omarwatt/MCU-with-Peripherals/DUT/EXECUTE.VHD

--============================================================================
-- Copyright 2026 Hananya Ribo 
-- Advanced CPU architecture and Hardware Accelerators Lab 361-1-4693 BGU
-- Execute module (implements the data ALU and Branch Address Adder) 
--============================================================================
LIBRARY IEEE;
USE IEEE.STD_LOGIC_1164.ALL;
USE IEEE.STD_LOGIC_ARITH.ALL;
USE IEEE.STD_LOGIC_SIGNED.ALL;
USE IEEE.NUMERIC_STD.ALL;
USE work.const_package.all;


ENTITY  Execute IS
	generic(
		DATA_BUS_WIDTH 	: integer := 32;
		MULT_WIDTH	 	: integer := 16;
		PC_WIDTH 		: integer := 10
	);
	PORT(	
		--Inputs
		read_data1_i 	: IN 	STD_LOGIC_VECTOR(DATA_BUS_WIDTH-1 DOWNTO 0);
		read_data2_i 	: IN 	STD_LOGIC_VECTOR(DATA_BUS_WIDTH-1 DOWNTO 0);
		sign_extend_i 	: IN 	STD_LOGIC_VECTOR(DATA_BUS_WIDTH-1 DOWNTO 0);
		UpperIm_ctrl_i	: IN 	STD_LOGIC_VECTOR(1 DOWNTO 0);
		ALUOp_ctrl_i	: IN 	STD_LOGIC_VECTOR(4 DOWNTO 0);
		MULOp_ctrl_i	: IN 	STD_LOGIC_VECTOR(1 DOWNTO 0);
		ALUSrc_ctrl_i 	: IN 	STD_LOGIC;
		pc_i			: IN 	STD_LOGIC_VECTOR(PC_WIDTH-1 DOWNTO 0);
		--Outputs
		brTaken_o 		: OUT	STD_LOGIC;
		mul_res_o 		: OUT	STD_LOGIC_VECTOR(DATA_BUS_WIDTH-1 DOWNTO 0);
		alu_res_o 		: OUT	STD_LOGIC_VECTOR(DATA_BUS_WIDTH-1 DOWNTO 0);
		addr_gen_o 		: OUT	STD_LOGIC_VECTOR(PC_WIDTH-1 DOWNTO 0)
	);
END Execute;


ARCHITECTURE struct OF Execute IS
	SIGNAL 	ain_w 					: STD_LOGIC_VECTOR(DATA_BUS_WIDTH-1 DOWNTO 0);
	SIGNAL 	bin_w 					: STD_LOGIC_VECTOR(DATA_BUS_WIDTH-1 DOWNTO 0);
	SIGNAL 	sub_res_w 			: STD_LOGIC_VECTOR(DATA_BUS_WIDTH-1 DOWNTO 0);
	SIGNAL 	ltu_res_w 			: STD_LOGIC;
	SIGNAL 	eq_res_w				: STD_LOGIC;
	SIGNAL	msbneq_res_w		: STD_LOGIC;
	SIGNAL	alu_res_r 			: STD_LOGIC_VECTOR(DATA_BUS_WIDTH-1 DOWNTO 0);
	SIGNAL	brTaken_w 			: STD_LOGIC;
	
	SIGNAL	brl_shl_s1_r		: STD_LOGIC_VECTOR(DATA_BUS_WIDTH-1 DOWNTO 0);
	SIGNAL	brl_shl_s2_r		: STD_LOGIC_VECTOR(DATA_BUS_WIDTH-1 DOWNTO 0);
	SIGNAL	brl_shl_s3_r		: STD_LOGIC_VECTOR(DATA_BUS_WIDTH-1 DOWNTO 0);
	SIGNAL	brl_shl_s4_r		: STD_LOGIC_VECTOR(DATA_BUS_WIDTH-1 DOWNTO 0);
	
	SIGNAL	brl_shr_s1_r		: STD_LOGIC_VECTOR(DATA_BUS_WIDTH-1 DOWNTO 0);
	SIGNAL	brl_shr_s2_r		: STD_LOGIC_VECTOR(DATA_BUS_WIDTH-1 DOWNTO 0);
	SIGNAL	brl_shr_s3_r		: STD_LOGIC_VECTOR(DATA_BUS_WIDTH-1 DOWNTO 0);
	SIGNAL	brl_shr_s4_r		: STD_LOGIC_VECTOR(DATA_BUS_WIDTH-1 DOWNTO 0);
	SIGNAL	brl_shr_pad_r		: STD_LOGIC_VECTOR(DATA_BUS_WIDTH-1 DOWNTO 0);
	
	SIGNAL P0_w, P1_w, P2_w, P3_w 	: STD_LOGIC_VECTOR(MULT_WIDTH-1 downto 0);
	SIGNAL al_w, ah_w, bl_w, bh_w 	: STD_LOGIC_VECTOR(7 downto 0);
	SIGNAL M_w 						: STD_LOGIC_VECTOR(16 downto 0);
	SIGNAL MULTI_res_r				: std_logic_vector(DATA_BUS_WIDTH-1 DOWNTO 0);
		
BEGIN
--------------------------------------------------------------------------------------------------------
-- Branch Address Adder
-- addr_gen_o = pc_i + (sign_extend_i << 2)
--------------------------------------------------------------------------------------------------------					  
addr_gen_o	<= pc_i(PC_WIDTH-1 DOWNTO 0) + (sign_extend_i(PC_WIDTH-3 DOWNTO 0) & '0');

--------------------------------------------------------------------------------------------------------
--ALU
--------------------------------------------------------------------------------------------------------
WITH UpperIm_ctrl_i SELECT
	ain_w <= 	read_data1_i																					WHEN	"00",
						((DATA_BUS_WIDTH-PC_WIDTH-1) DOWNTO 0 => '0') & pc_i	WHEN	"01",
						(others => '0')	WHEN	OTHERS;
	
bin_w <= 	read_data2_i	WHEN not ALUSrc_ctrl_i ELSE	sign_extend_i(DATA_BUS_WIDTH-1 DOWNTO 0);


--Reused resuls 
sub_res_w			<= ain_w - bin_w;
ltu_res_w			<= '1' WHEN ain_w < bin_w 					ELSE '0';
eq_res_w			<= '1' WHEN ain_w = bin_w 					ELSE '0'; 
msbneq_res_w		<= '1' WHEN ain_w(31) /= bin_w(31) 	ELSE '0';


al_w <= ain_w(7  downto 0)	when MULOp_ctrl_i = Multi_Mul else (others => '0');
ah_w <= ain_w(15 downto 8) 	when MULOp_ctrl_i = Multi_Mul else (others => '0');
bl_w <= bin_w(7  downto 0) 	when MULOp_ctrl_i = Multi_Mul else (others => '0');
bh_w <= bin_w(15 downto 8) 	when MULOp_ctrl_i = Multi_Mul else (others => '0');

P0_w <= al_w * bl_w;
P1_w <= al_w * bh_w;
P2_w <= ah_w * bl_w;
P3_w <= ah_w * bh_w;
M_w  <= ('0' & P1_w) + ('0' & P2_w);

PROCESS (all)
BEGIN
	-- default values
	alu_res_r 		<= (others => '0');
	MULTI_res_r 	<= (others => '0');
	brTaken_w 		<= '0';
	brl_shl_s1_r	<= (others => '0');
	brl_shl_s2_r	<= (others => '0');
	brl_shl_s3_r	<= (others => '0'); 
	brl_shl_s4_r	<= (others => '0');
	brl_shr_s1_r	<= (others => '0');
	brl_shr_s2_r	<= (others => '0');
	brl_shr_s3_r	<= (others => '0'); 
	brl_shr_s4_r	<= (others => '0');
	brl_shr_pad_r	<= (others => '0');
	
	
 	CASE ALUOp_ctrl_i IS	-- Select ALU operation
		------------------------------------------------------
    -- Arithmetic
    ------------------------------------------------------
		-- add, addi, auipc, jal, jalr
		WHEN ALU_ADD 	=>
			alu_res_r	<= ain_w + bin_w;
			brTaken_w	<= '0';
		
		-- sub
		WHEN ALU_SUB	=>
			alu_res_r	<= sub_res_w;		 
			brTaken_w	<= '0';
		------------------------------------------------------
    -- Logic
    ------------------------------------------------------
		-- and, andi	
    WHEN	ALU_AND 	=>
			alu_res_r	<= ain_w and bin_w;
			brTaken_w	<= '0';
		
		-- or, ori		
	 	WHEN ALU_OR	=>
			alu_res_r	<= ain_w or bin_w;
			brTaken_w	<= '0';
		
		-- xor, xori
		WHEN ALU_XOR 	=>
			alu_res_r	<= ain_w xor bin_w;
			brTaken_w	<= '0';
				
		------------------------------------------------------
    -- Shift Left
    ------------------------------------------------------
		-- sll, slli
 	 	WHEN ALU_SHIFTL	=>
			-- Barrel-Shifter SHL stage 0
			if (bin_w(0) = '1') then
				brl_shl_s1_r <= (ain_w(30 DOWNTO 0) & '0');
			else
				brl_shl_s1_r <= ain_w;
			end if;
					
			-- Barrel-Shifter SHL stage 1
			if (bin_w(1) = '1') then
				brl_shl_s2_r <= (brl_shl_s1_r(29 DOWNTO 0) & "00");
			else
				brl_shl_s2_r <= brl_shl_s1_r;
			end if;
					
			-- Barrel-Shifter SHL stage 2
			if (bin_w(2) = '1')	then
				brl_shl_s3_r <= (brl_shl_s2_r(27 DOWNTO 0) & "0000");
			else
				brl_shl_s3_r <= brl_shl_s2_r;
			end if;
					
			-- Barrel-Shifter SHL stage 3
			if (bin_w(3) = '1')	then
				brl_shl_s4_r <= (brl_shl_s3_r(23 DOWNTO 0) & "00000000");
			else
				brl_shl_s4_r <= brl_shl_s3_r;
			end if;
					
			-- Barrel-Shifter SHL stage 4
			if (bin_w(4) = '1')	then
				alu_res_r <= (brl_shl_s4_r(15 DOWNTO 0) & "0000000000000000");
			else
				alu_res_r <= brl_shl_s4_r;
			end if;
				      
			brTaken_w	<= '0';
		------------------------------------------------------
    -- Shift Right
    ------------------------------------------------------		
		-- srl, srli, sra, srai	
 	 	WHEN ALU_SHIFTR | ALU_SHIFTR_ARITH 	=>
			--if sra? pad with 1's else pad with 0's 
			if (ain_w(31) = '1' and (ALUOp_ctrl_i = ALU_SHIFTR_ARITH)) then
				brl_shr_pad_r <= 32x"FFFF";
			else
				brl_shr_pad_r <= 32x"0000";
			end if;
			
			-- Barrel-Shifter SHR stage 0
			if (bin_w(0) = '1') then
				brl_shr_s1_r <= (brl_shr_pad_r(31) & ain_w(31 DOWNTO 1));
			else
				brl_shr_s1_r <= ain_w;
			end if;
			
			-- Barrel-Shifter SHR stage 1
			if (bin_w(1) = '1') then
				brl_shr_s2_r <= (brl_shr_pad_r(31 DOWNTO 30) & brl_shr_s1_r(31 DOWNTO 2));
			else
				brl_shr_s2_r <= brl_shr_s1_r;
			end if;
			
			-- Barrel-Shifter SHR stage 2
			if (bin_w(2) = '1') then
				brl_shr_s3_r <= (brl_shr_pad_r(31 DOWNTO 28) & brl_shr_s2_r(31 DOWNTO 4));
			else
				brl_shr_s3_r <= brl_shr_s2_r;
			end if;
			
			-- Barrel-Shifter SHR stage 3
			if (bin_w(3) = '1') then
				brl_shr_s4_r <= (brl_shr_pad_r(31 DOWNTO 24) & brl_shr_s3_r(31 DOWNTO 8));
			else
				brl_shr_s4_r <= brl_shr_s3_r;
			end if;
			
			-- Barrel-Shifter SHR stage 4
			if (bin_w(4) = '1')	then
				alu_res_r <= (brl_shr_pad_r(31 DOWNTO 16) & brl_shr_s4_r(31 DOWNTO 16));
			else
				alu_res_r <= brl_shr_s4_r;
			end if;
				   
			brTaken_w	<= '0';		 	 				
		------------------------------------------------------
    -- Comparision
    ------------------------------------------------------
		-- slt, slti
		WHEN ALU_LESS_THAN_SIGNED	=>
			brTaken_w	<= '0';
			IF msbneq_res_w THEN
				IF ain_w(31) THEN
					alu_res_r	<= (0 => '1', others => '0');	--32'h1
				ELSE
					alu_res_r	<= (others => '0');						--32'h0
				END IF;
			ELSE
				IF sub_res_w(31) THEN
					alu_res_r	<= (0 => '1', others => '0');	--32'h1	
				ELSE
					alu_res_r	<= (others => '0');						--32'h0
				END IF;
			END IF;
		
		-- sltu, sltiu 
		WHEN ALU_LESS_THAN_UNSIGNED	=>
			brTaken_w	<= '0';
			IF ltu_res_w THEN
				alu_res_r	<= (0 => '1', others => '0');		--32'h1
			ELSE
				alu_res_r	<= (others => '0');							--32'h0
			END IF;

	------------------------------------------------------
    -- Condional Branch 
    ------------------------------------------------------
		-- beq
		WHEN ALU_BEQ	=>
			alu_res_r	<= (others => '0');
			brTaken_w	<= eq_res_w;
		
		-- bne
		WHEN ALU_BNE	=>
			alu_res_r	<= (others => '0');
			brTaken_w	<= not eq_res_w;
		
		-- blt
		WHEN ALU_BLT	=>
			alu_res_r	<= (others => '0');
			IF msbneq_res_w THEN
				brTaken_w	<= ain_w(31);
			ELSE
				brTaken_w	<= sub_res_w(31);
			END IF;
		
		-- bge
		WHEN ALU_BGE	=>
			alu_res_r	<= (others => '0');
			IF msbneq_res_w THEN
				brTaken_w	<= bin_w(31);
			ELSE
				brTaken_w	<= not sub_res_w(31);
			END IF;
		
		-- bltu
		WHEN ALU_BLTU	=>
			alu_res_r	<= (others => '0');
			brTaken_w	<= ltu_res_w;
		
		-- bgeu
		WHEN ALU_BGEU	=>
			alu_res_r	<= (others => '0');
			brTaken_w	<= not ltu_res_w;
		
 	 	WHEN OTHERS	=>
			alu_res_r	<= (others => '0');
			brTaken_w	<= '0';
  	END CASE;

	case MULOp_ctrl_i is
		when  Multi_Mul =>
			MULTI_res_r <= (X"0000" & P0_w) + ("0000000" & M_w & x"00") + (P3_w & x"0000");
		when others =>
			MULTI_res_r <= (others => '0');
	end case;

		
  
END PROCESS;
	
--------------------------------------------------------------------------------------------------------
brTaken_o	<= brTaken_w;

alu_res_o <= alu_res_r;

mul_res_o <= MULTI_res_r;


END struct;
