omarwatt/MCU-with-Peripherals/DUT/uart_rx.vhd

--------------------------------------------------------------------------------
-- PROJECT: SIMPLE UART FOR FPGA
--------------------------------------------------------------------------------
-- MODULE:  UART RECEIVER
-- AUTHORS: Jakub Cabal <jakubcabal@gmail.com>
-- LICENSE: The MIT License (MIT), please read LICENSE file
-- WEBSITE: https://github.com/jakubcabal/uart-for-fpga
--------------------------------------------------------------------------------

library IEEE;
use IEEE.STD_LOGIC_1164.ALL;
use IEEE.NUMERIC_STD.ALL;
use work.aux_package.all;

entity UART_RX is
    Port (
        CLK         : in  std_logic; -- system clock
        RST         : in  std_logic; -- high active synchronous reset
        -- UART INTERFACE
        UART_CLK_EN : in  std_logic; -- oversampling (16x) UART clock enable
        UART_RXD    : in  std_logic; -- serial receive data
        PENA_i      : in  std_logic; -- ADDED: UTCL parity enable
        PEV_i       : in  std_logic; -- ADDED: UTCL parity type
        -- USER DATA OUTPUT INTERFACE
        DOUT            : out std_logic_vector(7 downto 0); -- output data received via UART
        DOUT_VLD        : out std_logic; -- when DOUT_VLD = 1, output data (DOUT) are valid (is assert only for one clock cycle)
        FRAME_ERROR     : out std_logic;  -- when FRAME_ERROR = 1, stop bit was invalid (is assert only for one clock cycle)
        PARITY_ERROR    : out std_logic; 
        RX_BUSY_o       : out std_logic  
    );
end UART_RX;

architecture FULL of UART_RX is

    signal rx_clk_en          : std_logic;
    signal rx_ticks           : unsigned(3 downto 0);
    signal rx_clk_divider_en  : std_logic;
    signal rx_data            : std_logic_vector(7 downto 0);
    signal rx_bit_count       : unsigned(2 downto 0);
    signal rx_receiving_data  : std_logic;
    signal rx_parity_bit      : std_logic;
    signal rx_parity_error    : std_logic;
    signal rx_output_reg_en   : std_logic;


    type state is (idle, startbit, databits, paritybit, stopbit);
    signal rx_pstate : state;
    signal rx_nstate : state;

begin

    DOUT <= rx_data;
    RX_BUSY_o   <= '0' when rx_pstate = idle else '1';
    -- -------------------------------------------------------------------------
    -- UART RECEIVER CLOCK DIVIDER AND CLOCK ENABLE FLAG
    -- -------------------------------------------------------------------------
    uart_rx_clk_divider_p : process (CLK)
    begin
        if (rising_edge(CLK)) then
            if (rx_clk_divider_en = '1') then
                if (UART_CLK_EN = '1') then
                    if (rx_ticks = "1111") then
                        rx_ticks <= (others => '0');
                    else
                        rx_ticks <= rx_ticks + 1;
                    end if;
                else
                    rx_ticks <= rx_ticks;
                end if;
            else
                rx_ticks <= (others => '0');
            end if;
        end if;
    end process;

    uart_rx_clk_en_p : process (CLK)
    begin
        if (rising_edge(CLK)) then
            if (RST = '1') then
                rx_clk_en <= '0';
            elsif (UART_CLK_EN = '1' AND rx_ticks = "0111") then
                rx_clk_en <= '1';
            else
                rx_clk_en <= '0';
            end if;
        end if;
    end process;
    
    -- -------------------------------------------------------------------------
    -- UART RECEIVER BIT COUNTER
    -- -------------------------------------------------------------------------

    uart_rx_bit_counter_p : process (CLK)
    begin
        if (rising_edge(CLK)) then
            if (RST = '1') then
                rx_bit_count <= (others => '0');
            elsif (rx_clk_en = '1' AND rx_receiving_data = '1') then
                if (rx_bit_count = "111") then
                    rx_bit_count <= (others => '0');
                else
                    rx_bit_count <= rx_bit_count + 1;
                end if;
            end if;
        end if;
    end process;

    -- -------------------------------------------------------------------------
    -- UART RECEIVER DATA SHIFT REGISTER
    -- -------------------------------------------------------------------------

    uart_rx_data_shift_reg_p : process (CLK)
    begin
        if (rising_edge(CLK)) then
            if RST = '1' then
                rx_data <= (others => '0'); 
            elsif (rx_clk_en = '1' AND rx_receiving_data = '1') then
                rx_data <= UART_RXD & rx_data(7 downto 1);
            end if;
        end if;
    end process;


    -- -------------------------------------------------------------------------
    -- UART RECEIVER PARITY GENERATOR AND CHECK
    -- -------------------------------------------------------------------------

    uart_rx_parity_gen_i : entity work.UART_PARITY
        generic map (
            DATA_WIDTH => 8
        )
        port map (
            DATA_IN    => rx_data,
            PEV_i      => PEV_i,
            PARITY_OUT => rx_parity_bit
        ); 

    uart_rx_parity_check_reg_p : process (CLK)
    begin
        if (rising_edge(CLK)) then
            if (PENA_i = '0') then
                rx_parity_error <= '0';
            elsif (rx_clk_en = '1') then
                rx_parity_error <= rx_parity_bit XOR UART_RXD;
            end if;
        end if;
    end process;

    -- -------------------------------------------------------------------------
    -- UART RECEIVER OUTPUT REGISTER
    -- -------------------------------------------------------------------------

    uart_rx_output_reg_p : process (CLK)
    begin
        if (rising_edge(CLK)) then
            if (RST = '1') then
                DOUT_VLD        <= '0';
                FRAME_ERROR     <= '0';
                PARITY_ERROR    <= '0';
            else
                if (rx_clk_en = '1' AND rx_output_reg_en = '1') then
                    DOUT_VLD <= '1';
                    FRAME_ERROR <= NOT UART_RXD;
                    if PENA_i = '1' then
                        PARITY_ERROR <= rx_parity_error; -- make the error seperate from dout_vld
                    else
                        PARITY_ERROR <= '0';
                    end if;
                else
                    DOUT_VLD        <= '0';
                    FRAME_ERROR     <= '0';
                    PARITY_ERROR    <= '0';
                end if;
            end if;
        end if;
    end process;

    -- -------------------------------------------------------------------------
    -- UART RECEIVER FSM
    -- -------------------------------------------------------------------------

    -- PRESENT STATE REGISTER
    process (CLK)
    begin
        if (rising_edge(CLK)) then
            if (RST = '1') then
                rx_pstate <= idle;
            else
                rx_pstate <= rx_nstate;
            end if;
        end if;
    end process;

    -- NEXT STATE AND OUTPUTS LOGIC
    process (all)
    begin
        case rx_pstate is

            when idle =>
                rx_output_reg_en  <= '0';
                rx_receiving_data <= '0';
                rx_clk_divider_en <= '0';

                if (UART_RXD = '0') then
                    rx_nstate <= startbit;
                else
                    rx_nstate <= idle;
                end if;

            when startbit =>
                rx_output_reg_en  <= '0';
                rx_receiving_data <= '0';
                rx_clk_divider_en <= '1';

                if (rx_clk_en = '1') then
                    rx_nstate <= databits;
                else
                    rx_nstate <= startbit;
                end if;

            when databits =>
                rx_output_reg_en  <= '0';
                rx_receiving_data <= '1';
                rx_clk_divider_en <= '1';

                if ((rx_clk_en = '1') AND (rx_bit_count = "111")) then
                    if (PENA_i = '0') then
                        rx_nstate <= stopbit;
                    else
                        rx_nstate <= paritybit;
                    end if ;
                else
                    rx_nstate <= databits;
                end if;

            when paritybit =>
                rx_output_reg_en  <= '0';
                rx_receiving_data <= '0';
                rx_clk_divider_en <= '1';

                if (rx_clk_en = '1') then
                    rx_nstate <= stopbit;
                else
                    rx_nstate <= paritybit;
                end if;

            when stopbit =>
                rx_output_reg_en  <= '1';
                rx_receiving_data <= '0';
                rx_clk_divider_en <= '1';

                if (rx_clk_en = '1') then
                    rx_nstate <= idle;
                else
                    rx_nstate <= stopbit;
                end if;

            when others =>
                rx_output_reg_en  <= '0';
                rx_receiving_data <= '0';
                rx_clk_divider_en <= '0';
                rx_nstate         <= idle;

        end case;
    end process;

end FULL;
