omarwatt/MCU-with-Peripherals/DUT/uart_tx.vhd

--------------------------------------------------------------------------------
-- PROJECT: SIMPLE UART FOR FPGA
--------------------------------------------------------------------------------
-- MODULE:  UART TRANSMITTER
-- AUTHORS: Jakub Cabal <jakubcabal@gmail.com>
-- LICENSE: The MIT License (MIT), please read LICENSE file
-- WEBSITE: https://github.com/jakubcabal/uart-for-fpga
--------------------------------------------------------------------------------

library IEEE;
use IEEE.STD_LOGIC_1164.ALL;
use IEEE.NUMERIC_STD.ALL;
use work.aux_package.all;

entity UART_TX is
    Port (
        CLK         : in  std_logic; -- system clock
        RST         : in  std_logic; -- high active synchronous reset
        -- UART INTERFACE
        UART_CLK_EN : in  std_logic; -- oversampling (16x) UART clock enable
        UART_TXD    : out std_logic; -- serial transmit data
        -- USER DATA INPUT INTERFACE
        DIN         : in  std_logic_vector(7 downto 0); -- input data to be transmitted over UART
        DIN_VLD     : in  std_logic; -- when DIN_VLD = 1, input data (DIN) are valid
        DIN_RDY     : out std_logic;  -- when DIN_RDY = 1, transmitter is ready and valid input data will be accepted for transmiting
       
        PENA_i        : in  std_logic; 
        PEV_i         : in  std_logic;
        TX_BUSY_o     : out std_logic
    );
end UART_TX;

architecture FULL of UART_TX is

    signal tx_clk_en         : std_logic;
    signal tx_clk_divider_en : std_logic;
    signal tx_ticks          : unsigned(3 downto 0);
    signal tx_data           : std_logic_vector(7 downto 0);
    signal tx_bit_count      : unsigned(2 downto 0);
    signal tx_bit_count_en   : std_logic;
    signal tx_ready          : std_logic;
    signal tx_parity_bit     : std_logic;
    signal tx_data_out_sel   : std_logic_vector(1 downto 0);

    type state is (idle, txsync, startbit, databits, paritybit, stopbit);
    signal tx_pstate : state;
    signal tx_nstate : state;

begin

    DIN_RDY     <= tx_ready;
    TX_BUSY_o   <= '0' when tx_pstate = idle else '1';
    -- -------------------------------------------------------------------------
    -- UART TRANSMITTER CLOCK DIVIDER
    -- -------------------------------------------------------------------------

    uart_tx_clk_divider_p : process (CLK)
    begin
        if (rising_edge(CLK)) then
            if (tx_clk_divider_en = '1') then
                if (uart_clk_en = '1') then
                    if (tx_ticks = "1111") then
                        tx_ticks <= (others => '0');
                    else
                        tx_ticks <= tx_ticks + 1;
                    end if;
                else
                    tx_ticks <= tx_ticks;
                end if;
            else
                tx_ticks <= (others => '0');
            end if;
        end if;
    end process;

    uart_tx_clk_en_p : process (CLK)
    begin
        if (rising_edge(CLK)) then
            if (RST = '1') then
                tx_clk_en <= '0';
            elsif (uart_clk_en = '1' AND tx_ticks = "0001") then
                tx_clk_en <= '1';
            else
                tx_clk_en <= '0';
            end if;
        end if;
    end process;

    -- -------------------------------------------------------------------------
    -- UART TRANSMITTER INPUT DATA REGISTER
    -- -------------------------------------------------------------------------

    uart_tx_input_data_reg_p : process (CLK)
    begin
        if (rising_edge(CLK)) then
            if RST = '1' then
                tx_data     <= (others => '0') ;
            elsif (DIN_VLD = '1' AND tx_ready = '1') then
                tx_data     <= DIN;
            end if;
        end if;
    end process;
    -- -------------------------------------------------------------------------
    -- UART TRANSMITTER BIT COUNTER
    -- -------------------------------------------------------------------------

    uart_tx_bit_counter_p : process (CLK)
    begin
        if (rising_edge(CLK)) then
            if (RST = '1') then
                tx_bit_count <= (others => '0');
            elsif (tx_bit_count_en = '1' AND tx_clk_en = '1') then
                if (tx_bit_count = "111") then
                    tx_bit_count <= (others => '0');
                else
                    tx_bit_count <= tx_bit_count + 1;
                end if;
            end if;
        end if;
    end process;

    -- -------------------------------------------------------------------------
    -- UART TRANSMITTER PARITY GENERATOR
    -- -------------------------------------------------------------------------

        uart_tx_parity_gen_i: entity work.UART_PARITY
        generic map (
            DATA_WIDTH  => 8
        )
        port map (
            DATA_IN     => tx_data,
            PEV_i       => PEV_i,
            PARITY_OUT  => tx_parity_bit
        );
   

    -- uart_tx_noparity_g : if (PARITY_BIT = "none") generate
    --     tx_parity_bit <= '0';
    -- end generate;

    -- -------------------------------------------------------------------------
    -- UART TRANSMITTER OUTPUT DATA REGISTER
    -- -------------------------------------------------------------------------

    uart_tx_output_data_reg_p : process (CLK)
    begin
        if (rising_edge(CLK)) then
            if (RST = '1') then
                UART_TXD <= '1';
            else
                case tx_data_out_sel is
                    when "01" => -- START BIT
                        UART_TXD <= '0';
                    when "10" => -- DATA BITS
                        UART_TXD <= tx_data(to_integer(tx_bit_count));
                    when "11" => -- PARITY BIT
                        UART_TXD <= tx_parity_bit;
                    when others => -- STOP BIT OR IDLE
                        UART_TXD <= '1';
                end case;
            end if;
        end if;
    end process;

    -- -------------------------------------------------------------------------
    -- UART TRANSMITTER FSM
    -- -------------------------------------------------------------------------

    -- PRESENT STATE REGISTER
    process (CLK)
    begin
        if (rising_edge(CLK)) then
            if (RST = '1') then
                tx_pstate <= idle;
            else
                tx_pstate <= tx_nstate;
            end if;
        end if;
    end process;

    -- NEXT STATE AND OUTPUTS LOGIC
    process (all)
    begin

        case tx_pstate is

            when idle =>
                tx_ready <= '1';
                tx_data_out_sel <= "00";
                tx_bit_count_en <= '0';
                tx_clk_divider_en <= '0';

                if (DIN_VLD = '1') then
                    tx_nstate <= txsync;
                else
                    tx_nstate <= idle;
                end if;

            when txsync =>
                tx_ready <= '0';
                tx_data_out_sel <= "00";
                tx_bit_count_en <= '0';
                tx_clk_divider_en <= '1';

                if (tx_clk_en = '1') then
                    tx_nstate <= startbit;
                else
                    tx_nstate <= txsync;
                end if;

            when startbit =>
                tx_ready <= '0';
                tx_data_out_sel <= "01";
                tx_bit_count_en <= '0';
                tx_clk_divider_en <= '1';

                if (tx_clk_en = '1') then
                    tx_nstate <= databits;
                else
                    tx_nstate <= startbit;
                end if;

            when databits =>
                tx_ready <= '0';
                tx_data_out_sel <= "10";
                tx_bit_count_en <= '1';
                tx_clk_divider_en <= '1';

                if ((tx_clk_en = '1') AND (tx_bit_count = "111")) then
                    if (PENA_i = '1') then
                        tx_nstate <= paritybit;
                    else
                        tx_nstate <= stopbit;
                    end if ;
                else
                    tx_nstate <= databits;
                end if;

            when paritybit =>
                tx_ready <= '0';
                tx_data_out_sel <= "11";
                tx_bit_count_en <= '0';
                tx_clk_divider_en <= '1';

                if (tx_clk_en = '1') then
                    tx_nstate <= stopbit;
                else
                    tx_nstate <= paritybit;
                end if;

            when stopbit =>
                tx_ready <= '0';
                tx_data_out_sel <= "00";
                tx_bit_count_en <= '0';
                tx_clk_divider_en <= '1';

                if (tx_clk_en = '1') then
                    tx_nstate <= idle;
                else
                    tx_nstate <= stopbit;
                end if;

            when others =>
                tx_ready <= '0';
                tx_data_out_sel <= "00";
                tx_bit_count_en <= '0';
                tx_clk_divider_en <= '0';
                tx_nstate <= idle;

        end case;
    end process;

end FULL;
