omarwatt/MCU-with-Peripherals/TB/BasicTimer_tb.vhd

library ieee;
use ieee.std_logic_1164.all;

entity BasicTimer_tb is
end BasicTimer_tb;

architecture sim of BasicTimer_tb is

    signal SMCLK        : std_logic := '0';
    signal rst          : std_logic := '1';
    signal Address      : std_logic_vector(5 downto 0) := (others => '0');
    signal MemRead      : std_logic := '0';
    signal MemWrite     : std_logic := '0';
    signal CAPIN1       : std_logic := '0';
    signal CAPIN2       : std_logic := '0';

    signal DataBus      : std_logic_vector(31 downto 0);
    signal TB_Data      : std_logic_vector(31 downto 0) := (others => '0');
    signal TB_BusEnable : std_logic := '0';

    signal PWM          : std_logic;
    signal BTIFG        : std_logic;
    signal BTCAPR       : std_logic_vector(31 downto 0);

begin

    SMCLK <= not SMCLK after 5 ns;

    DataBus <= TB_Data when TB_BusEnable = '1'
               else (others => 'Z');

    DUT : entity work.BasicTimer
        port map (
            SMCLK_i    => SMCLK,
            rst_i      => rst,
            Address_i  => Address,
            DataBus_io => DataBus,
            MemRead_i  => MemRead,
            MemWrite_i => MemWrite,
            CAPIN1_i   => CAPIN1,
            CAPIN2_i   => CAPIN2,
            PWM_o      => PWM,
            BTIFG_o    => BTIFG,
            BTCAPR_o   => BTCAPR
        );

    process
    begin
        --------------------------------------------------
        -- Test 1: BTCMPR0 = 2
        --------------------------------------------------
        rst <= '1';
        wait for 20 ns;
        rst <= '0';

        Address      <= "110000";
        TB_Data      <= x"00000002";
        TB_BusEnable <= '1';
        MemWrite     <= '1';
        wait until falling_edge(SMCLK);
        MemWrite     <= '0';
        TB_BusEnable <= '0';

        Address      <= "101110";
        TB_Data      <= x"00000000";
        TB_BusEnable <= '1';
        MemWrite     <= '1';
        wait until falling_edge(SMCLK);
        MemWrite     <= '0';
        TB_BusEnable <= '0';

        wait for 220 ns;

        --------------------------------------------------
        -- Test 2: BTCMPR0 = 4
        --------------------------------------------------
        rst <= '1';
        wait for 20 ns;
        rst <= '0';

        Address      <= "110000";
        TB_Data      <= x"00000004";
        TB_BusEnable <= '1';
        MemWrite     <= '1';
        wait until falling_edge(SMCLK);
        MemWrite     <= '0';
        TB_BusEnable <= '0';

        Address      <= "101110";
        TB_Data      <= x"00000000";
        TB_BusEnable <= '1';
        MemWrite     <= '1';
        wait until falling_edge(SMCLK);
        MemWrite     <= '0';
        TB_BusEnable <= '0';

        wait for 220 ns;

        --------------------------------------------------
        -- Test 3: BTCMPR0 = 6
        --------------------------------------------------
        rst <= '1';
        wait for 20 ns;
        rst <= '0';

        Address      <= "110000";
        TB_Data      <= x"00000006";
        TB_BusEnable <= '1';
        MemWrite     <= '1';
        wait until falling_edge(SMCLK);
        MemWrite     <= '0';
        TB_BusEnable <= '0';

        Address      <= "101110";
        TB_Data      <= x"00000000";
        TB_BusEnable <= '1';
        MemWrite     <= '1';
        wait until falling_edge(SMCLK);
        MemWrite     <= '0';
        TB_BusEnable <= '0';

        wait for 220 ns;

        --------------------------------------------------
        -- Test 4: BTCMPR0 = 8
        --------------------------------------------------
        rst <= '1';
        wait for 20 ns;
        rst <= '0';

        Address      <= "110000";
        TB_Data      <= x"00000008";
        TB_BusEnable <= '1';
        MemWrite     <= '1';
        wait until falling_edge(SMCLK);
        MemWrite     <= '0';
        TB_BusEnable <= '0';

        Address      <= "101110";
        TB_Data      <= x"00000000";
        TB_BusEnable <= '1';
        MemWrite     <= '1';
        wait until falling_edge(SMCLK);
        MemWrite     <= '0';
        TB_BusEnable <= '0';

        wait for 220 ns;

        --------------------------------------------------
        -- Test 5: BTCMPR0 = 10
        --------------------------------------------------
        rst <= '1';
        wait for 20 ns;
        rst <= '0';

        Address      <= "110000";
        TB_Data      <= x"0000000A";
        TB_BusEnable <= '1';
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

        Address      <= "101110";
        TB_Data      <= x"00000000";
        TB_BusEnable <= '1';
        MemWrite     <= '1';
        wait until falling_edge(SMCLK);
        MemWrite     <= '0';
        TB_BusEnable <= '0';

        wait for 220 ns;

        wait;
    end process;

end sim;
