omarwatt/MCU-with-Peripherals/DUT/SSD.vhd

library ieee;
use ieee.std_logic_1164.all;

entity SSD is
    port (
        ABCD_i : in STD_LOGIC_VECTOR(3 downto 0);
        Hex_o  : out STD_LOGIC_VECTOR(6 downto 0)
    );
end SSD;

architecture rtl of SSD is
begin
    with ABCD_i select
        Hex_o   <=  "1000000" when "0000", --0
                    "1111001" when "0001", --1 
                    "0100100" when "0010", --2
                    "0110000" when "0011", --3 
                    "0011001" when "0100", --4 
                    "0010010" when "0101", --5 
                    "0000010" when "0110", --6 
                    "1111000" when "0111", --7 
                    "0000000" when "1000", --8
                    "0011001" when "1001", --9 
                    "0001000" when "1010", --A 
                    "1000111" when "1011", --B 
                    "1000110" when "1100", --C 
                    "0100001" when "1101", --D 
                    "0000110" when "1110", --E 
                    "0001110" when "1111", --F 
                    (others => '1') when others; 

end rtl;
